iz8dwf/DataIO_29B_1Meg/img/DSCN2334.JPG

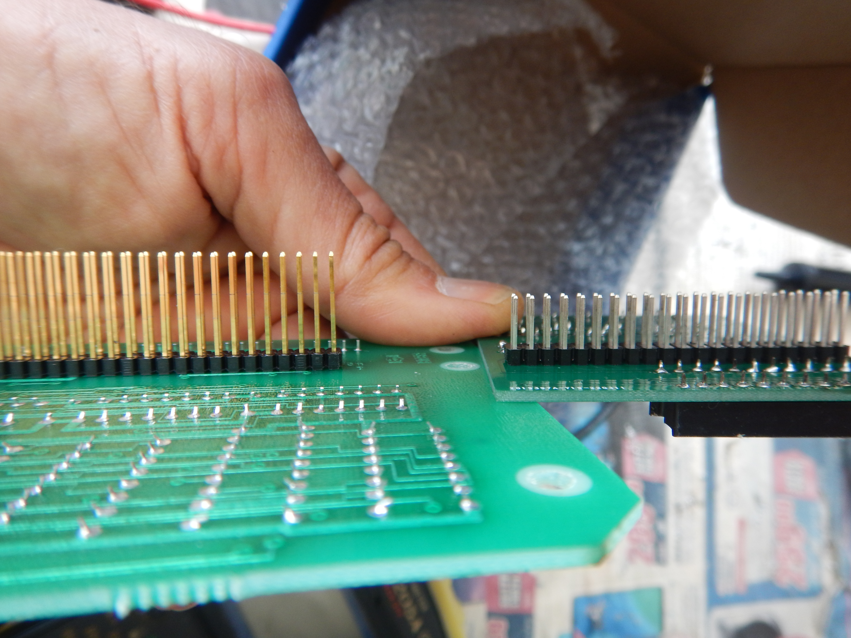
img/DSCN2334.JPG
